Quphoria/BenchATX/ATX PSU Bench Supply.kicad_sch

## KiCad design ATX PSU Bench Supply.kicad_sch (2026-05-01)

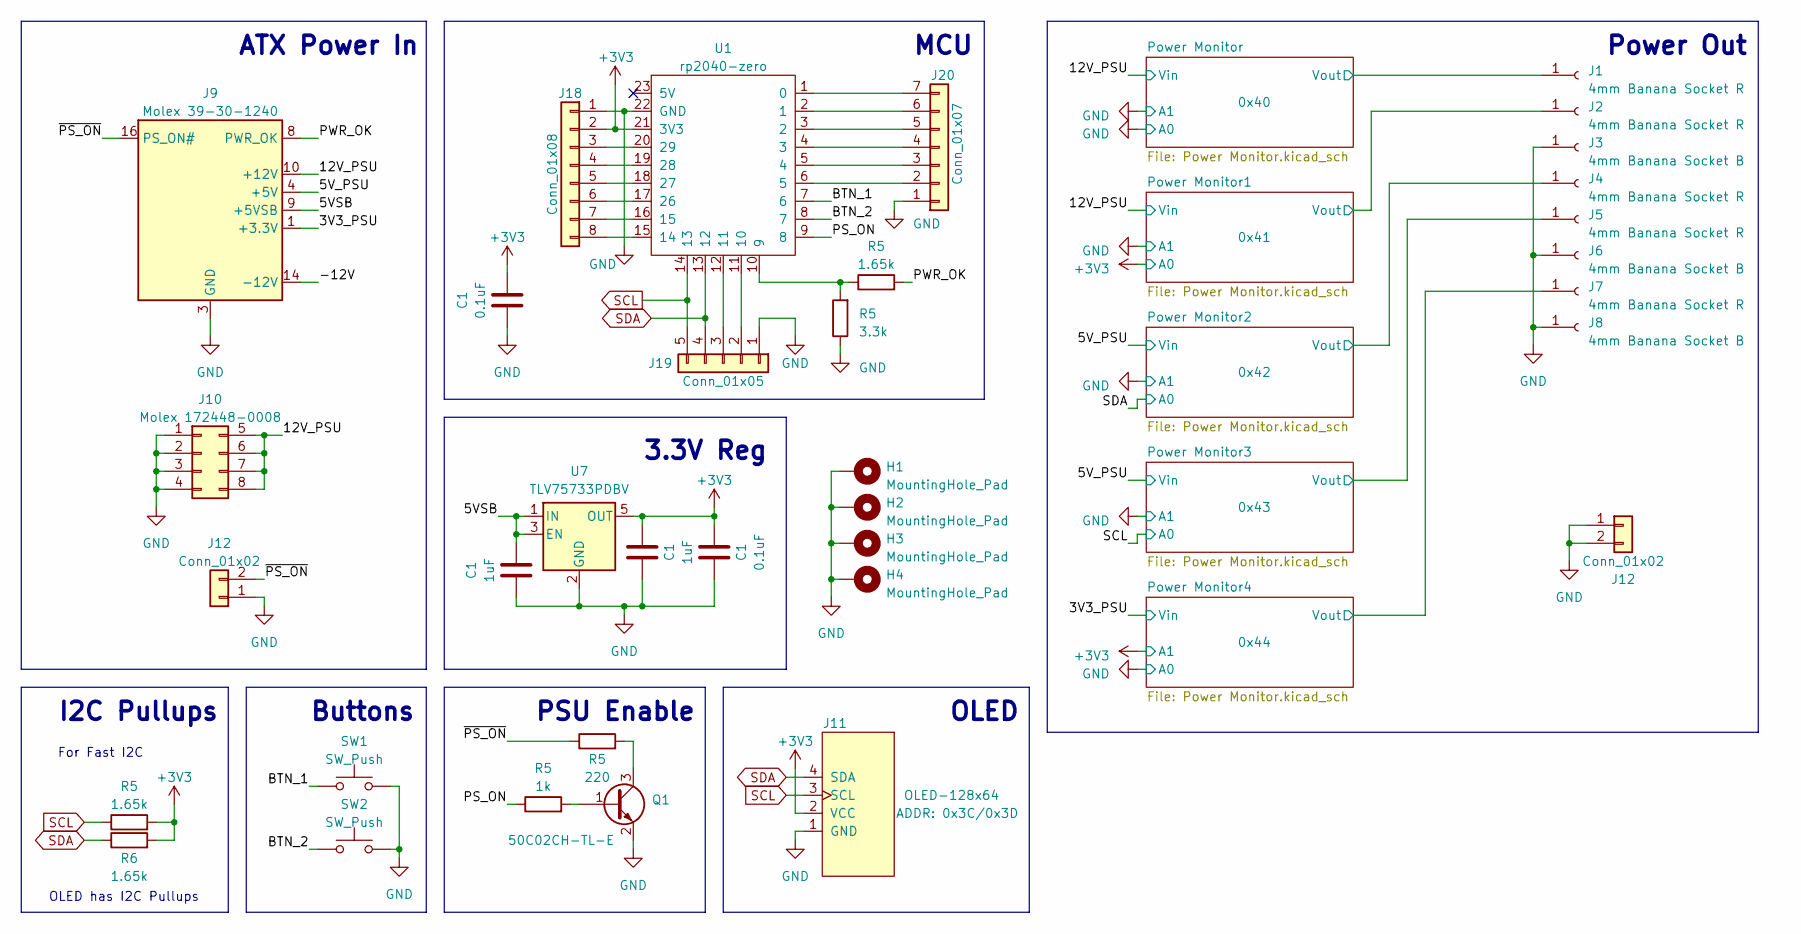
[picture p12: schematic ATX PSU Bench Supply.kicad_sch]

Parts:
C1: 1uF; C_0805_2012Metric_Pad1.18x1.45mm_HandSolder; Mouser No 581-KGM21AR71C105JU
H1, H2, H3, H4: MountingHole_Pad; MountingHole_3.2mm_M3_Pad_Via
J1, J2, J4, J5, J7: 4mm Banana Socket R; 24.243.1
J3, J6, J8: 4mm Banana Socket B; 24.243.2
J9: Molex 39-30-1240; Molex_Mini-Fit_Jr_5569-24A2_2x12_P4.20mm_Horizontal; Mouser No 538-39-30-1240
J10: Molex 172448-0008; Molex_Mini-Fit_Jr_5569-08A2_2x04_P4.20mm_Horizontal; Mouser No 538-172448-0008
J11: OLED-128x64
J12: Conn_01x02; PinSocket_1x02_P2.54mm_Vertical
J18: Conn_01x08; PinSocket_1x08_P2.54mm_Vertical
J19: Conn_01x05; PinSocket_1x05_P2.54mm_Vertical
J20: Conn_01x07; PinSocket_1x07_P2.54mm_Vertical
Q1: 50C02CH-TL-E; SOT-23_Handsoldering; Mouser No 863-50C02CH-TL-E
R5: 3.3k; R_0805_2012Metric_Pad1.20x1.40mm_HandSolder; Mouser No 71-CRCW0805-3.3K-E3
R6: 1.65k; R_0805_2012Metric_Pad1.20x1.40mm_HandSolder; Mouser No 71-CRCW0805-1.65K-E3
SW1, SW2: SW_Push; SW_PUSH_6mm; Mouser No 688-SKHHBW
U1: rp2040-zero; rp2040-zero-tht
U7: TLV75733PDBV; SOT-23-5; Mouser No 595-TLV75733PDBVR

Connections:
3V3_PSU: J9.1 (+3.3V), J9.2 (+3.3V), J9.12 (+3.3V), J9.13 (+3.3V)
5VSB: C1.1, J9.9 (+5VSB), U7.1 (IN), U7.3 (EN)
5V_PSU: J9.4 (+5V), J9.6 (+5V), J9.21 (+5V), J9.22 (+5V), J9.23 (+5V)
12V_PSU: J9.10 (+12V), J9.11 (+12V), J10.5, J10.6, J10.7, J10.8
+3V3: C1.1, J11.2 (VCC), J18.2, R5.2, R6.2, U1.21 (3V3), U7.5 (OUT)
-12V: J9.14 (-12V)
BTN_1: SW1.1, U1.7 (6)
BTN_2: SW2.1, U1.8 (7)
GND: C1.2, H1.1, H2.1, H3.1, H4.1, J3.1, J6.1, J8.1, J9.3 (GND), J9.5 (GND), J9.7 (GND), J9.15 (GND), J9.17 (GND), J9.18 (GND), J9.19 (GND), J9.24 (GND), J10.1, J10.2, J10.3, J10.4, J11.1 (GND), J12.1, J12.2, J18.1, J19.1, J20.1, Q1.2 (E), R5.1, SW1.2, SW2.2, U1.22 (GND), U7.2 (GND)
unnamed: J18.3, U1.20 (29)
unnamed: J18.4, U1.19 (28)
unnamed: J18.5, U1.18 (27)
unnamed: J18.6, U1.17 (26)
unnamed: J18.7, U1.16 (15)
unnamed: J18.8, U1.15 (14)
unnamed: J19.2, U1.11 (10)
unnamed: J19.3, U1.12 (11)
unnamed: J20.2, U1.6 (5)
unnamed: J20.3, U1.5 (4)
unnamed: J20.4, U1.4 (3)
unnamed: J20.5, U1.3 (2)
unnamed: J20.6, U1.2 (1)
unnamed: J20.7, U1.1 (0)
unnamed: Q1.1 (B), R5.2
unnamed: Q1.3 (C), R5.2
unnamed: R5.1, R5.2, U1.10 (9)
PS_ON: R5.1, U1.9 (8)
PWR_OK: J9.8 (PWR_OK), R5.2
SCL: J11.3 (SCL), J19.5, R5.1, U1.14 (13)
SDA: J11.4 (SDA), J19.4, R6.1, U1.13 (12)
Vout: J1.1, J2.1, J4.1, J5.1, J7.1
~PS_ON: J9.16 (PS_ON#), J12.2, R5.1

Notes on the sheet:
PSU Enable
MCU
ATX Power In
I2C Pullups
Buttons
3.3V Reg
Power Out
OLED
OLED has I2C Pullups
For Fast I2C
