Quphoria/BenchATX/Power Monitor.kicad_sch

## KiCad design Power Monitor.kicad_sch (2026-05-01)

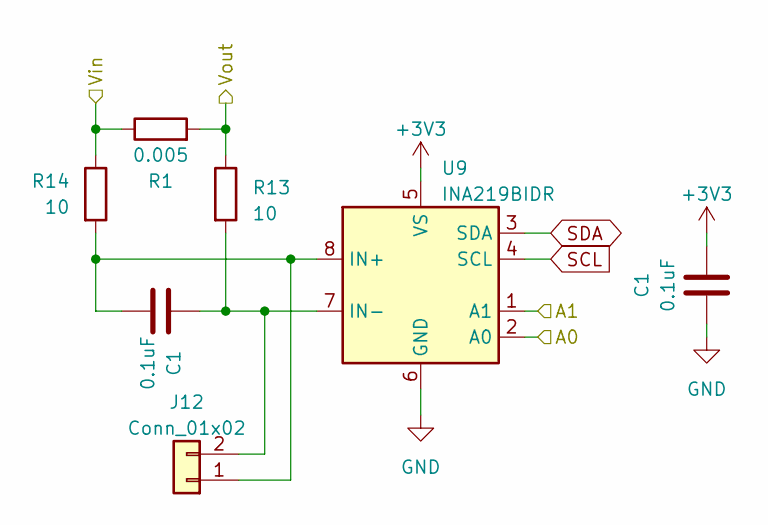
[picture p13: schematic Power Monitor.kicad_sch]

Parts:
C1: 0.1uF; C_0805_2012Metric_Pad1.18x1.45mm_HandSolder; Mouser No 581-08055C104J
J12: Conn_01x02; PinSocket_1x02_P2.54mm_Vertical
R1: 0.005; R_2512_6332Metric_Pad1.40x3.35mm_HandSolder; Mouser No 504-MSMA2512R0050FEN
R13, R14: 10; R_0805_2012Metric_Pad1.20x1.40mm_HandSolder; Mouser No 71-CRCW0805-10-E3
U9: INA219BIDR; SOIC-8_3.9x4.9mm_P1.27mm; Mouser No 595-INA219BIDR

Connections:
+3V3: C1.1, U9.5 (VS)
A0: U9.2 (A0)
A1: U9.1 (A1)
GND: C1.2, U9.6 (GND)
unnamed: C1.1, J12.1, R14.2, U9.8 (IN+)
unnamed: C1.2, J12.2, R13.2, U9.7 (IN-)
SCL: U9.4 (SCL)
SDA: U9.3 (SDA)
Vin: R1.1, R14.1
Vout: R1.2, R13.1
